FelixTrujillo/ESP32-DAQ/DAQ-Interface/Assets/Chart And Graph/Textures/back_black.png

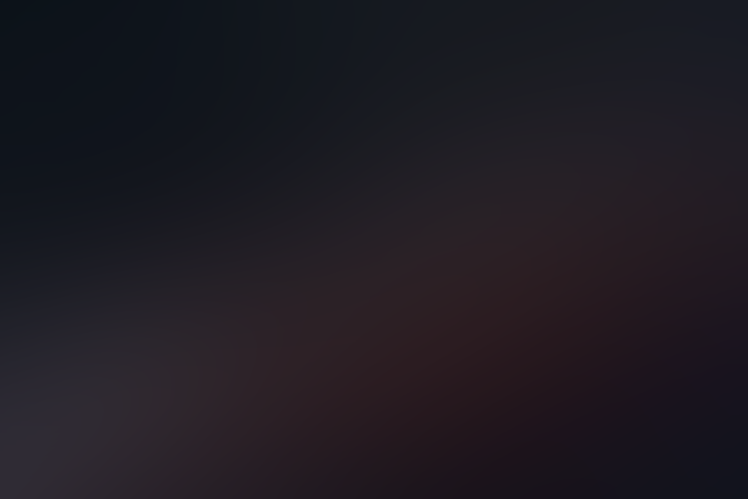
DAQ-Interface/Assets/Chart And Graph/Textures/back_black.png
