FelixTrujillo/ESP32-DAQ/DAQ-Interface/Assets/Chart And Graph/Textures/back_paper.png

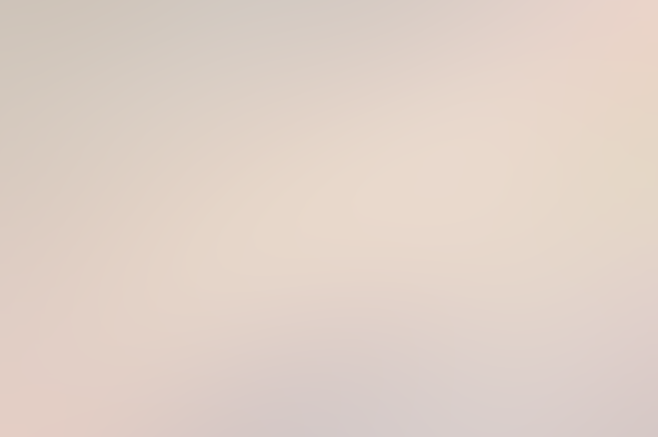
DAQ-Interface/Assets/Chart And Graph/Textures/back_paper.png
