FelixTrujillo/ESP32-DAQ/DAQ-Interface/Assets/Chart And Graph/Textures/background2.png

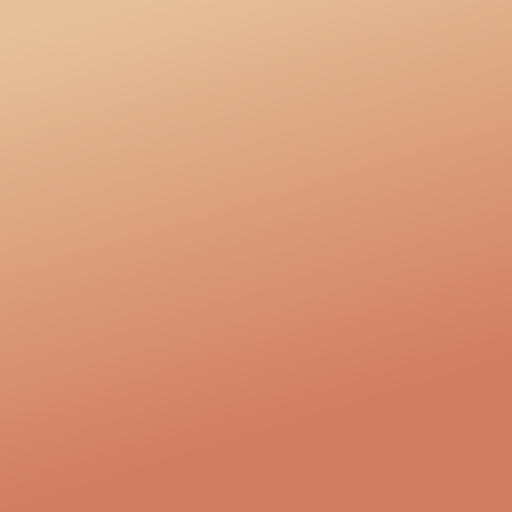
DAQ-Interface/Assets/Chart And Graph/Textures/background2.png
