FelixTrujillo/ESP32-DAQ/DAQ-Interface/Assets/Chart And Graph/Textures/backround2.png

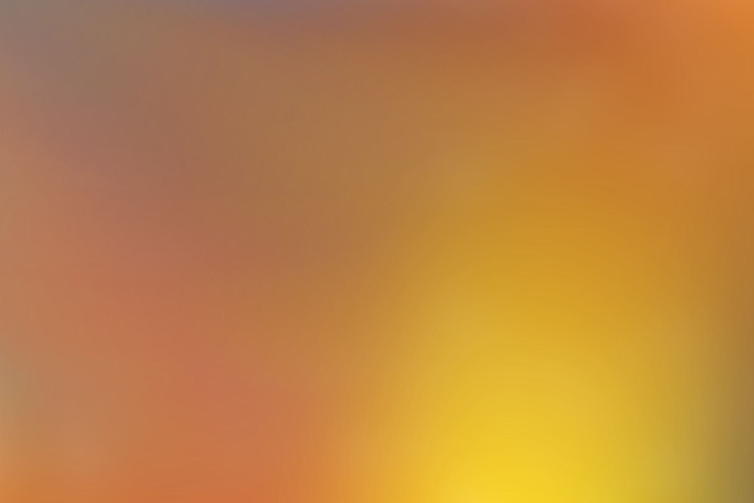
DAQ-Interface/Assets/Chart And Graph/Textures/backround2.png
