FelixTrujillo/ESP32-DAQ/DAQ-Interface/Assets/Chart And Graph/Textures/backround4.png

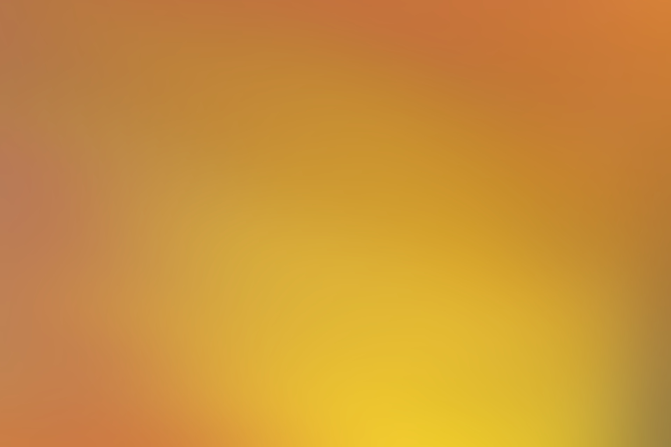
DAQ-Interface/Assets/Chart And Graph/Textures/backround4.png
