FelixTrujillo/ESP32-DAQ/DAQ-Interface/Assets/Chart And Graph/Textures/backround5.png

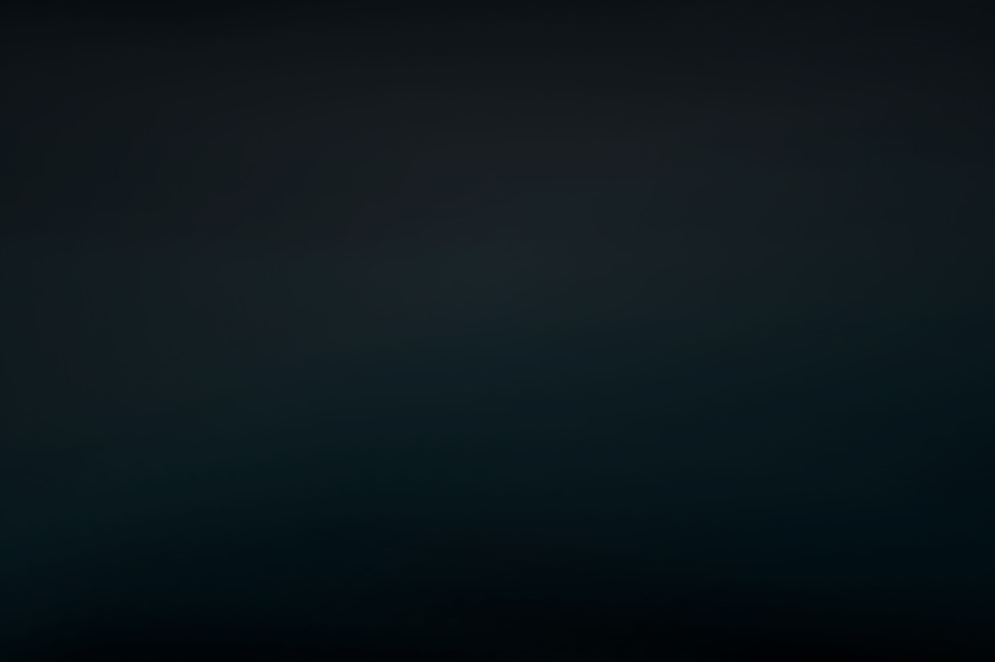
DAQ-Interface/Assets/Chart And Graph/Textures/backround5.png
