FelixTrujillo/ESP32-DAQ/DAQ-Interface/Assets/Chart And Graph/Textures/Bars/bar2.png

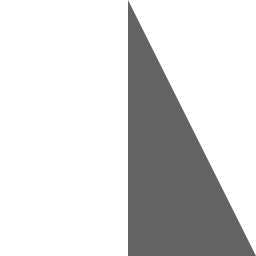
DAQ-Interface/Assets/Chart And Graph/Textures/Bars/bar2.png
