FelixTrujillo/ESP32-DAQ/DAQ-Interface/Assets/Chart And Graph/Textures/Bars/bar4.png

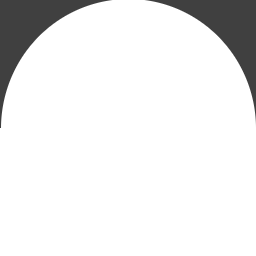
DAQ-Interface/Assets/Chart And Graph/Textures/Bars/bar4.png
