FelixTrujillo/ESP32-DAQ/DAQ-Interface/Assets/Chart And Graph/Textures/pieShade2.png

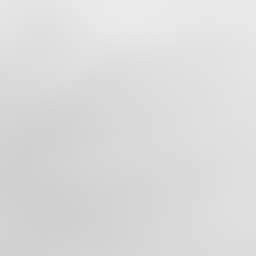
DAQ-Interface/Assets/Chart And Graph/Textures/pieShade2.png
