FelixTrujillo/ESP32-DAQ/DAQ-Interface/Assets/Chart And Graph/Textures/Points/CirclePoint.png

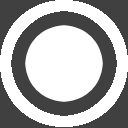
DAQ-Interface/Assets/Chart And Graph/Textures/Points/CirclePoint.png
