FelixTrujillo/ESP32-DAQ/DAQ-Interface/Assets/Chart And Graph/Textures/Points/Shade.png

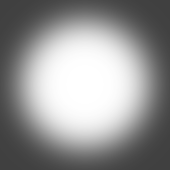
DAQ-Interface/Assets/Chart And Graph/Textures/Points/Shade.png
