FelixTrujillo/ESP32-DAQ/DAQ-Interface/Assets/Chart And Graph/Textures/Points/SimplePoint.png

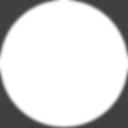
DAQ-Interface/Assets/Chart And Graph/Textures/Points/SimplePoint.png
