FelixTrujillo/ESP32-DAQ/DAQ-Interface/Assets/Chart And Graph/Themes/Common/Textures/borderPoint.png

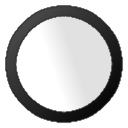
DAQ-Interface/Assets/Chart And Graph/Themes/Common/Textures/borderPoint.png
