FelixTrujillo/ESP32-DAQ/DAQ-Interface/Assets/Chart And Graph/Themes/Common/Textures/cc0-license/content/earth-earth-at-night-night-lights-41949.png

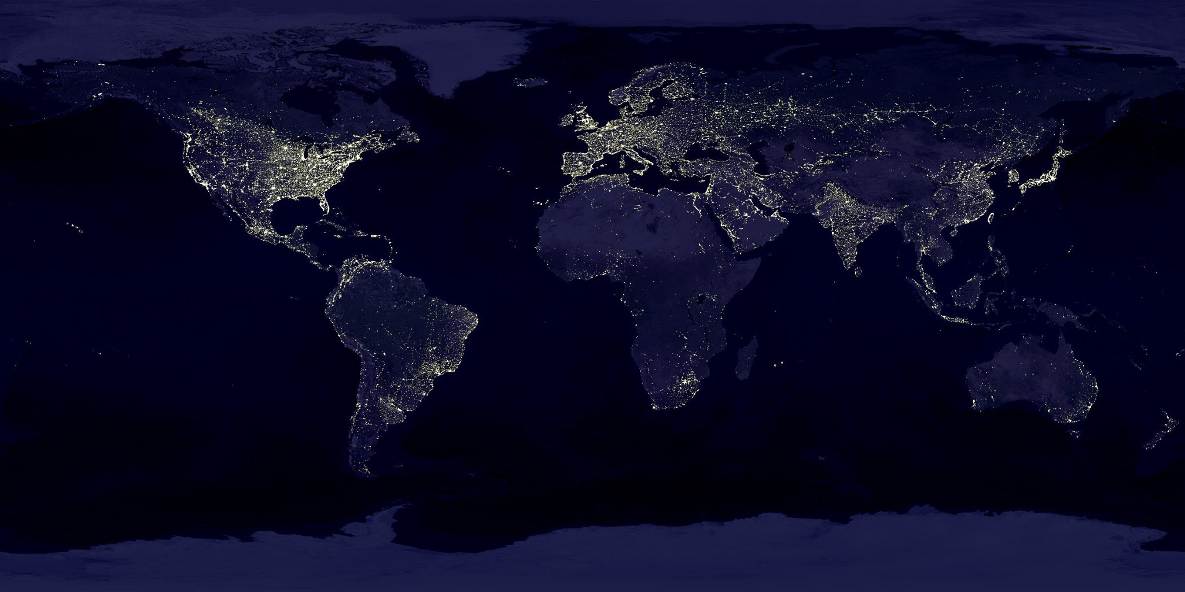
DAQ-Interface/Assets/Chart And Graph/Themes/Common/Textures/cc0-license/content/earth-earth-at-night-night-lights-41949.png
