FelixTrujillo/ESP32-DAQ/DAQ-Interface/Assets/Chart And Graph/Themes/Common/Textures/cc0-license/content/light-abstract-fire-heat.png

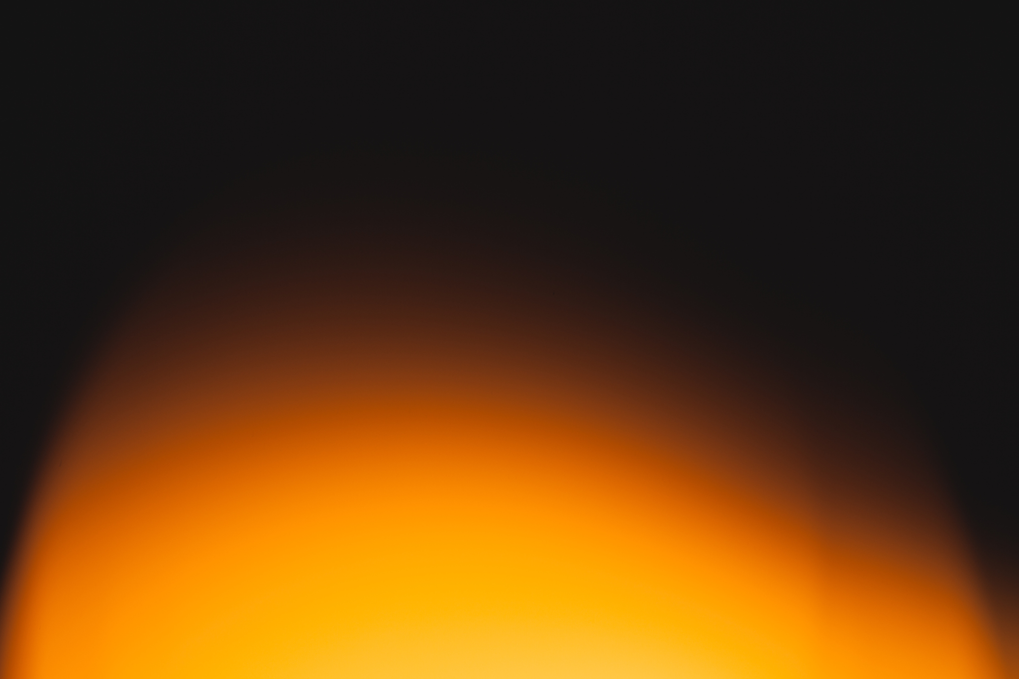
DAQ-Interface/Assets/Chart And Graph/Themes/Common/Textures/cc0-license/content/light-abstract-fire-heat.png
