FelixTrujillo/ESP32-DAQ/DAQ-Interface/Assets/Chart And Graph/Themes/Common/Textures/cc0-license/content/pexels-photo (1).png

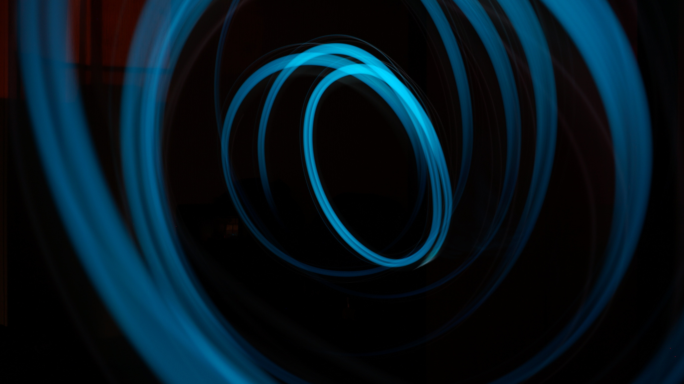
DAQ-Interface/Assets/Chart And Graph/Themes/Common/Textures/cc0-license/content/pexels-photo (1).png
