FelixTrujillo/ESP32-DAQ/DAQ-Interface/Assets/Chart And Graph/Themes/Common/Textures/cc0-license/content/yellow_notebook_paper_by_orangedotgreen.png

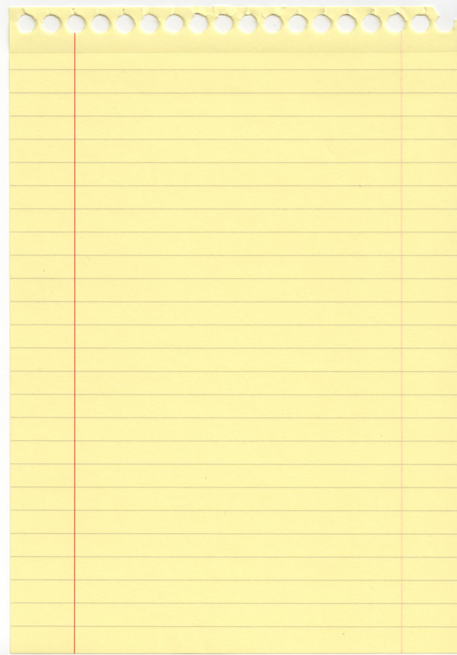
DAQ-Interface/Assets/Chart And Graph/Themes/Common/Textures/cc0-license/content/yellow_notebook_paper_by_orangedotgreen.png
