FelixTrujillo/ESP32-DAQ/DAQ-Interface/Assets/Chart And Graph/Themes/Common/Textures/T_Grid_floor2.png

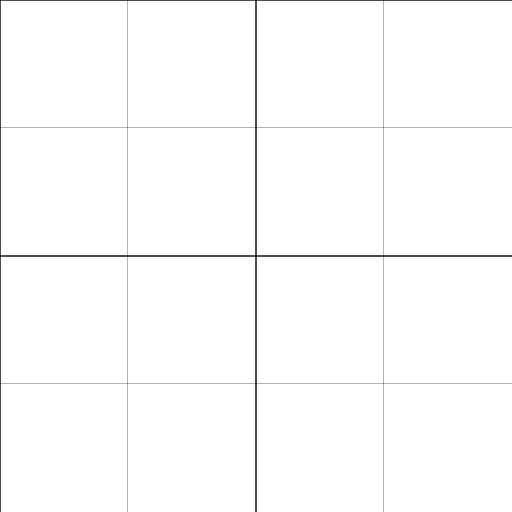
DAQ-Interface/Assets/Chart And Graph/Themes/Common/Textures/T_Grid_floor2.png
