FelixTrujillo/ESP32-DAQ/DAQ-Interface/Assets/Chart And Graph/Themes/Common/Textures/T_Hex.png

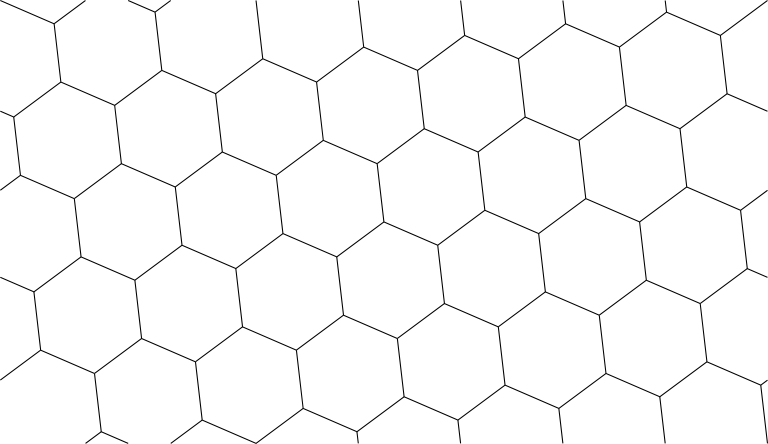
DAQ-Interface/Assets/Chart And Graph/Themes/Common/Textures/T_Hex.png
