FelixTrujillo/ESP32-DAQ/DAQ-Interface/Assets/Dark UI/Free/32 Light 2.png

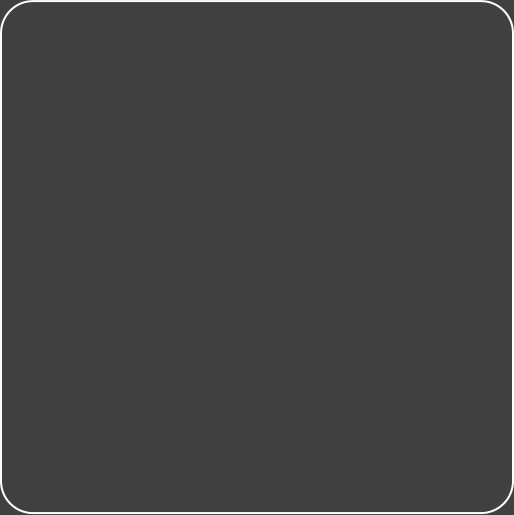
DAQ-Interface/Assets/Dark UI/Free/32 Light 2.png
