FelixTrujillo/ESP32-DAQ/DAQ-Interface/Assets/Dark UI/Free/128 Light 2.png

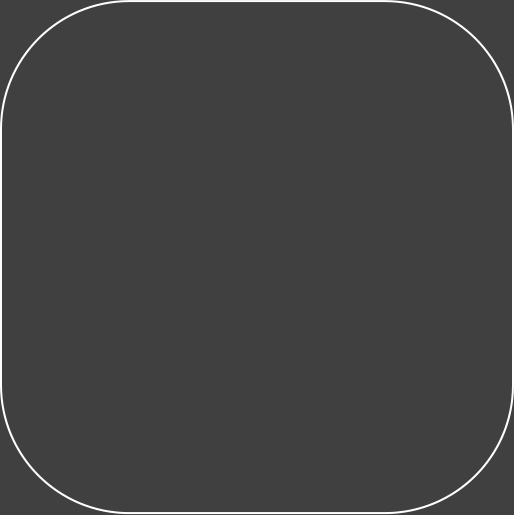
DAQ-Interface/Assets/Dark UI/Free/128 Light 2.png
