FelixTrujillo/ESP32-DAQ/DAQ-Interface/Assets/Dark UI/Free/Bell.png

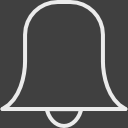
DAQ-Interface/Assets/Dark UI/Free/Bell.png
