FelixTrujillo/ESP32-DAQ/DAQ-Interface/Assets/Dark UI/Free/CIRCLE2PXLAR.png

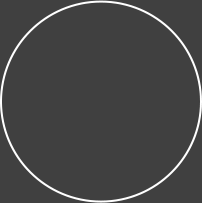
DAQ-Interface/Assets/Dark UI/Free/CIRCLE2PXLAR.png
