FelixTrujillo/ESP32-DAQ/DAQ-Interface/Assets/Dark UI/Free/Close BTN.png

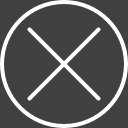
DAQ-Interface/Assets/Dark UI/Free/Close BTN.png
