FelixTrujillo/ESP32-DAQ/DAQ-Interface/Assets/Dark UI/Free/Coin.png

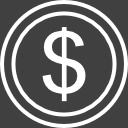
DAQ-Interface/Assets/Dark UI/Free/Coin.png
