FelixTrujillo/ESP32-DAQ/DAQ-Interface/Assets/Dark UI/Free/Down Arrow.png

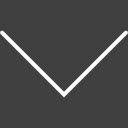
DAQ-Interface/Assets/Dark UI/Free/Down Arrow.png
