FelixTrujillo/ESP32-DAQ/DAQ-Interface/Assets/Dark UI/Free/Down BTN.png

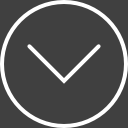
DAQ-Interface/Assets/Dark UI/Free/Down BTN.png
