FelixTrujillo/ESP32-DAQ/DAQ-Interface/Assets/Dark UI/Free/Facebook 2.png

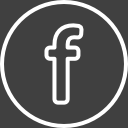
DAQ-Interface/Assets/Dark UI/Free/Facebook 2.png
