FelixTrujillo/ESP32-DAQ/DAQ-Interface/Assets/Dark UI/Free/Facebook.png

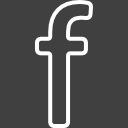
DAQ-Interface/Assets/Dark UI/Free/Facebook.png
