FelixTrujillo/ESP32-DAQ/DAQ-Interface/Assets/Dark UI/Free/Gem.png

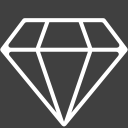
DAQ-Interface/Assets/Dark UI/Free/Gem.png
