FelixTrujillo/ESP32-DAQ/DAQ-Interface/Assets/Dark UI/Free/Heart.png

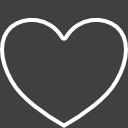
DAQ-Interface/Assets/Dark UI/Free/Heart.png
