FelixTrujillo/ESP32-DAQ/DAQ-Interface/Assets/Dark UI/Free/Info.png

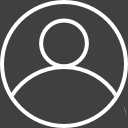
DAQ-Interface/Assets/Dark UI/Free/Info.png
