FelixTrujillo/ESP32-DAQ/DAQ-Interface/Assets/Dark UI/Free/Left Arrow.png

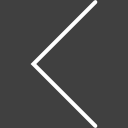
DAQ-Interface/Assets/Dark UI/Free/Left Arrow.png
