FelixTrujillo/ESP32-DAQ/DAQ-Interface/Assets/Dark UI/Free/Left BTN.png

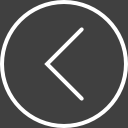
DAQ-Interface/Assets/Dark UI/Free/Left BTN.png
