FelixTrujillo/ESP32-DAQ/DAQ-Interface/Assets/Dark UI/Free/Lock.png

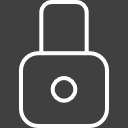
DAQ-Interface/Assets/Dark UI/Free/Lock.png
