FelixTrujillo/ESP32-DAQ/DAQ-Interface/Assets/Dark UI/Free/Messages.png

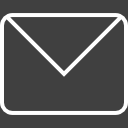
DAQ-Interface/Assets/Dark UI/Free/Messages.png
