FelixTrujillo/ESP32-DAQ/DAQ-Interface/Assets/Dark UI/Free/Missions.png

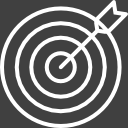
DAQ-Interface/Assets/Dark UI/Free/Missions.png
