FelixTrujillo/ESP32-DAQ/DAQ-Interface/Assets/Dark UI/Free/Music.png

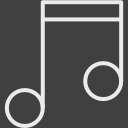
DAQ-Interface/Assets/Dark UI/Free/Music.png
