FelixTrujillo/ESP32-DAQ/DAQ-Interface/Assets/Dark UI/Free/Ranks.png

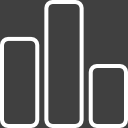
DAQ-Interface/Assets/Dark UI/Free/Ranks.png
