FelixTrujillo/ESP32-DAQ/DAQ-Interface/Assets/Dark UI/Free/Right Arrow.png

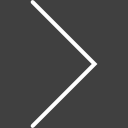
DAQ-Interface/Assets/Dark UI/Free/Right Arrow.png
