FelixTrujillo/ESP32-DAQ/DAQ-Interface/Assets/Dark UI/Free/Right BTN.png

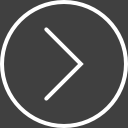
DAQ-Interface/Assets/Dark UI/Free/Right BTN.png
