FelixTrujillo/ESP32-DAQ/DAQ-Interface/Assets/Dark UI/Free/Settings.png

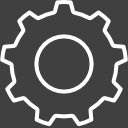
DAQ-Interface/Assets/Dark UI/Free/Settings.png
