FelixTrujillo/ESP32-DAQ/DAQ-Interface/Assets/Dark UI/Free/Shop.png

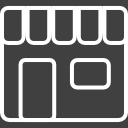
DAQ-Interface/Assets/Dark UI/Free/Shop.png
