FelixTrujillo/ESP32-DAQ/DAQ-Interface/Assets/Dark UI/Free/Sound.png

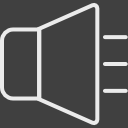
DAQ-Interface/Assets/Dark UI/Free/Sound.png
