FelixTrujillo/ESP32-DAQ/DAQ-Interface/Assets/Dark UI/Free/Star.png

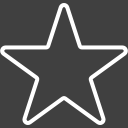
DAQ-Interface/Assets/Dark UI/Free/Star.png
