FelixTrujillo/ESP32-DAQ/DAQ-Interface/Assets/Dark UI/Free/Up Arrow.png

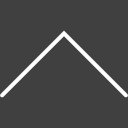
DAQ-Interface/Assets/Dark UI/Free/Up Arrow.png
