FelixTrujillo/ESP32-DAQ/DAQ-Interface/Assets/Dark UI/Free/Up BTN.png

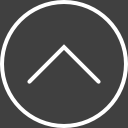
DAQ-Interface/Assets/Dark UI/Free/Up BTN.png
