FelixTrujillo/ESP32-DAQ/DAQ-Interface/Assets/Dark UI/Free/World.png

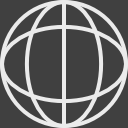
DAQ-Interface/Assets/Dark UI/Free/World.png
