FelixTrujillo/ESP32-DAQ/DAQ-Interface/Assets/Dark UI/Free/X.png

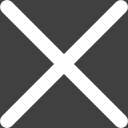
DAQ-Interface/Assets/Dark UI/Free/X.png
