FelixTrujillo/ESP32-DAQ/DAQ-Interface/Assets/Images/Bicineta_general.jpeg

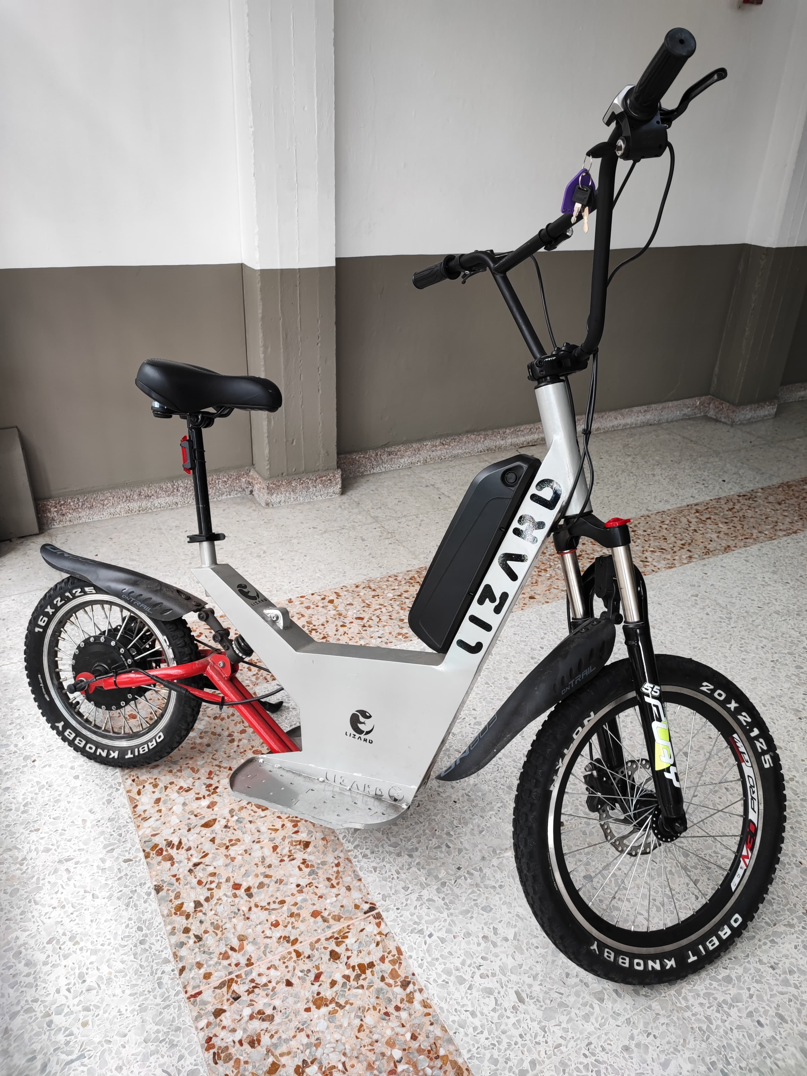
DAQ-Interface/Assets/Images/Bicineta_general.jpeg
