FelixTrujillo/ESP32-DAQ/Documentation/Images/Bicineta_backward.jpeg

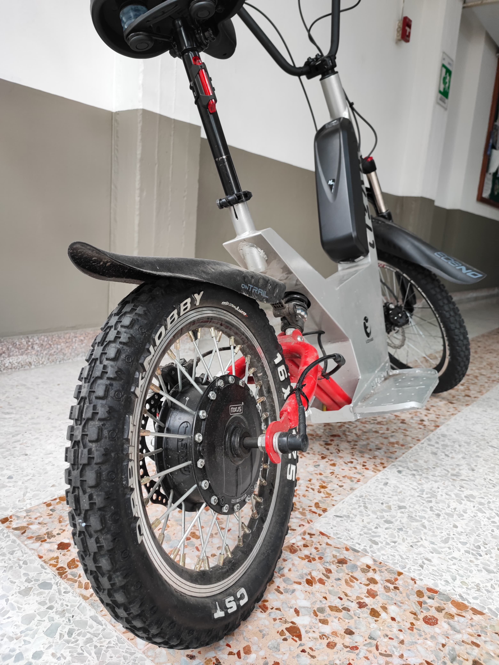
Documentation/Images/Bicineta_backward.jpeg
