FelixTrujillo/ESP32-DAQ/Documentation/Images/Bicineta_forward.jpeg

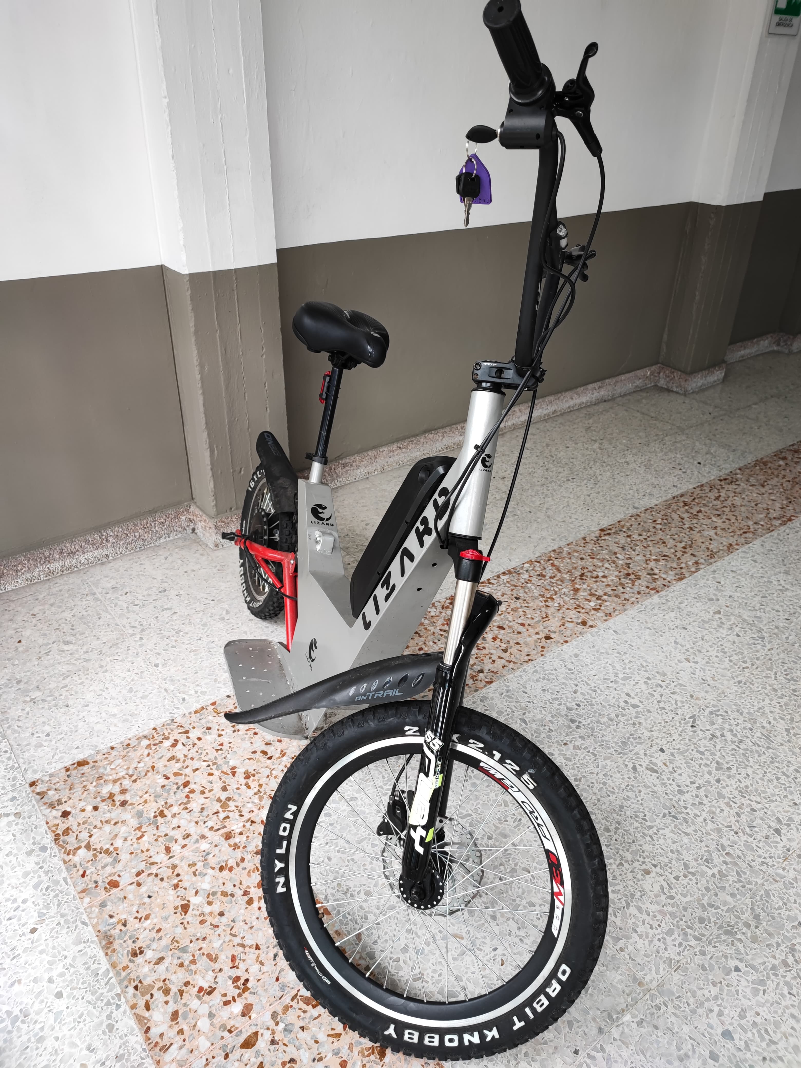
Documentation/Images/Bicineta_forward.jpeg
