FelixTrujillo/ESP32-DAQ/Documentation/Images/DAQ-Bicineta_render.png

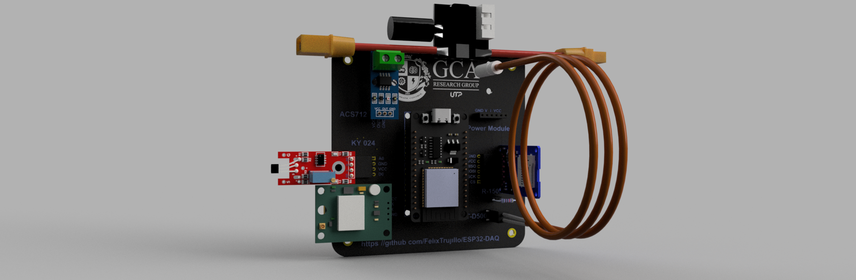
Documentation/Images/DAQ-Bicineta_render.png
