FelixTrujillo/ESP32-DAQ/Documentation/Images/DAQ_Bicineta_backward.jpeg

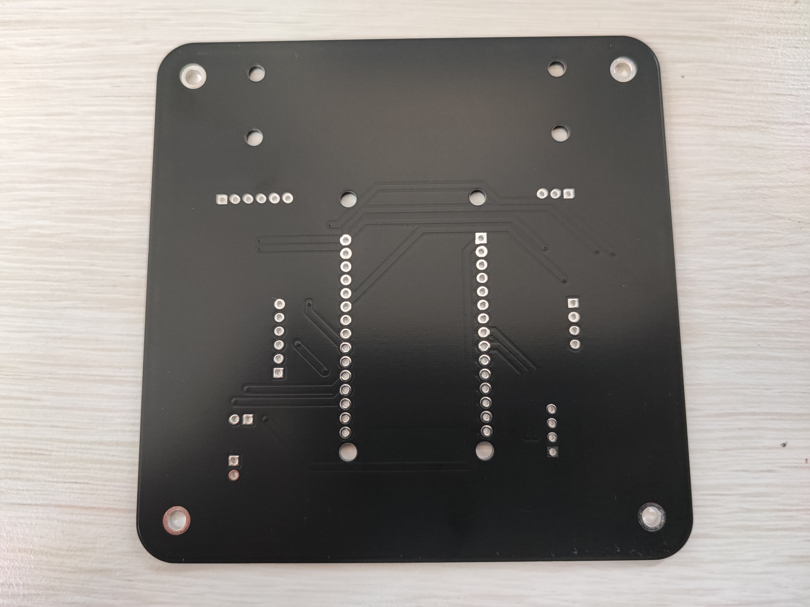
Documentation/Images/DAQ_Bicineta_backward.jpeg
