FelixTrujillo/ESP32-DAQ/Documentation/Images/DAQ_Bicineta_forward.jpeg

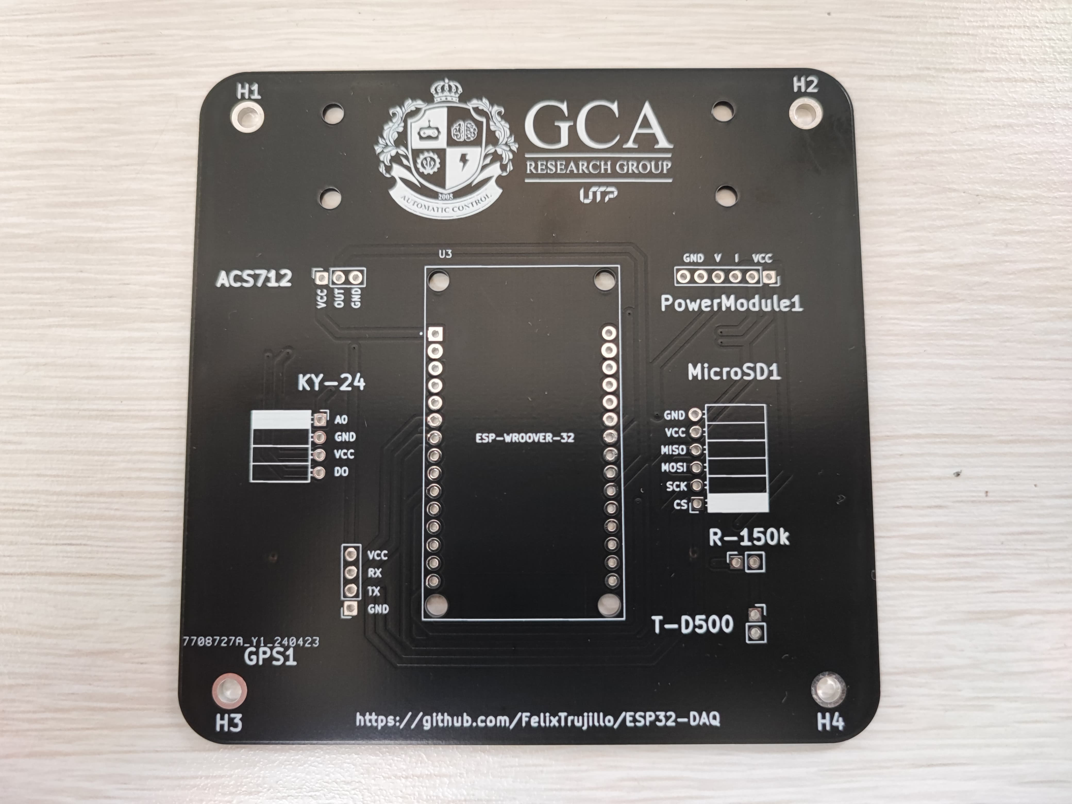
Documentation/Images/DAQ_Bicineta_forward.jpeg
