FelixTrujillo/ESP32-DAQ/Documentation/Images/Intarface/acceleration.png

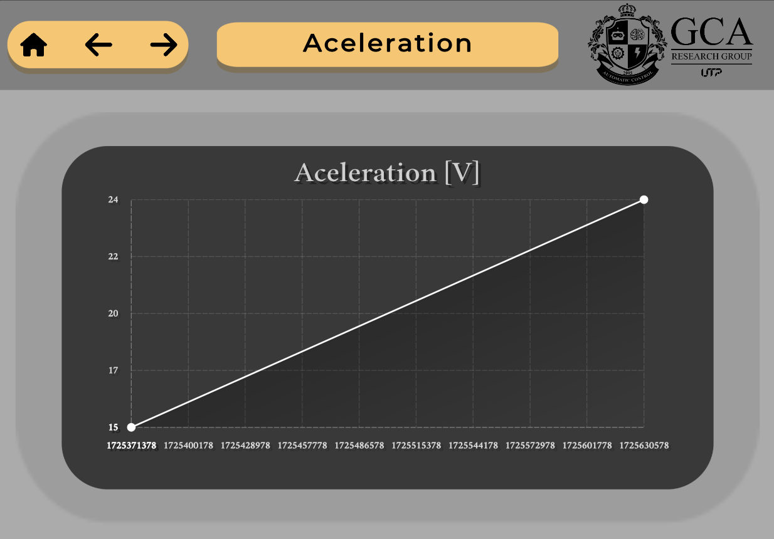
Documentation/Images/Intarface/acceleration.png
