FelixTrujillo/ESP32-DAQ/Documentation/Images/Intarface/brokerConfig.png

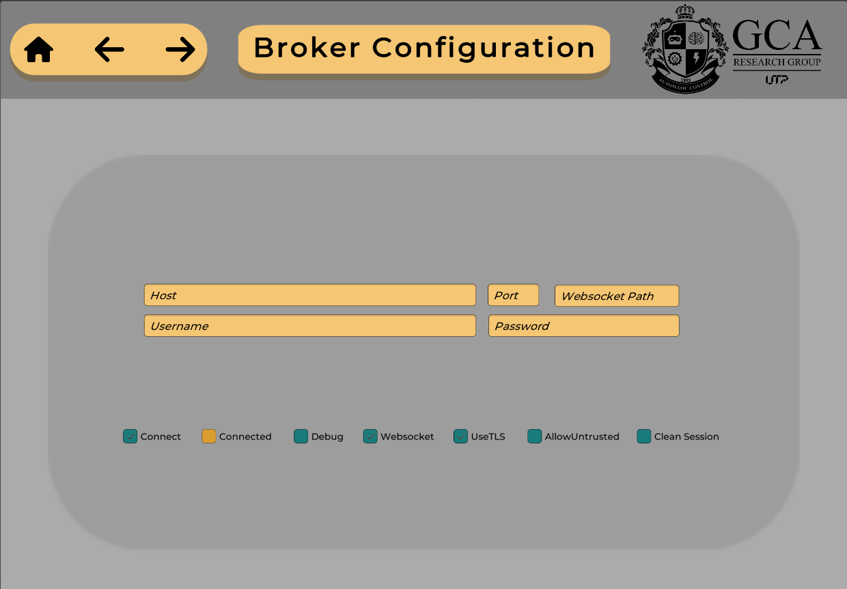
Documentation/Images/Intarface/brokerConfig.png
