FelixTrujillo/ESP32-DAQ/Documentation/Images/Intarface/current.png

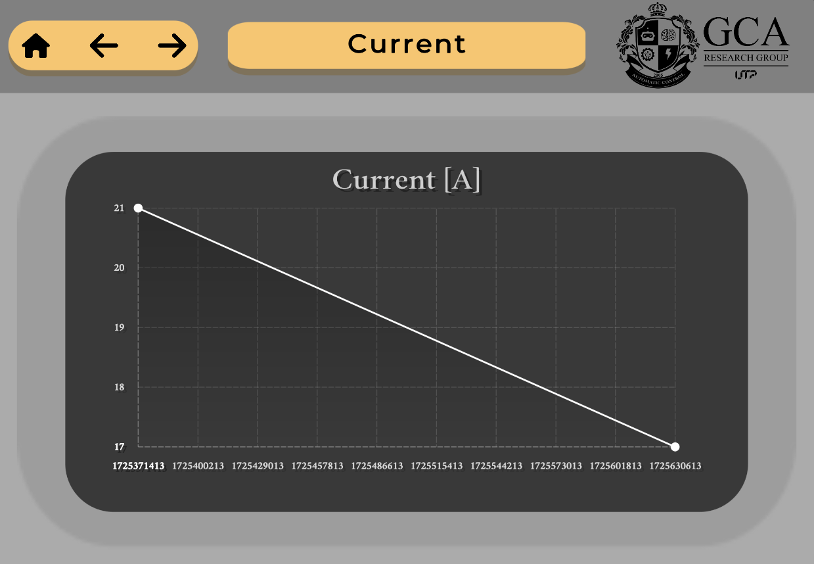
Documentation/Images/Intarface/current.png
