FelixTrujillo/ESP32-DAQ/Documentation/Images/Intarface/generalInformation.png

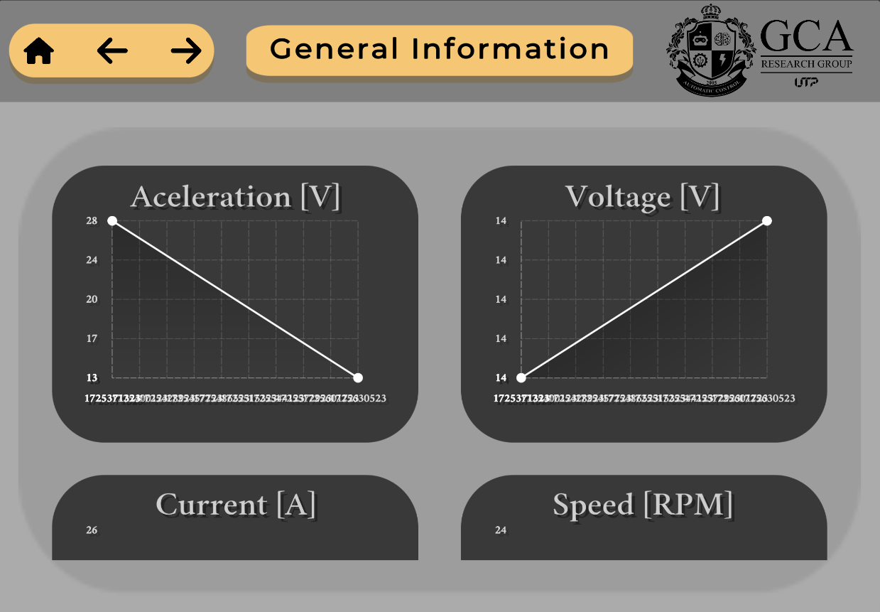
Documentation/Images/Intarface/generalInformation.png
