FelixTrujillo/ESP32-DAQ/Documentation/Images/Intarface/Loggin.png

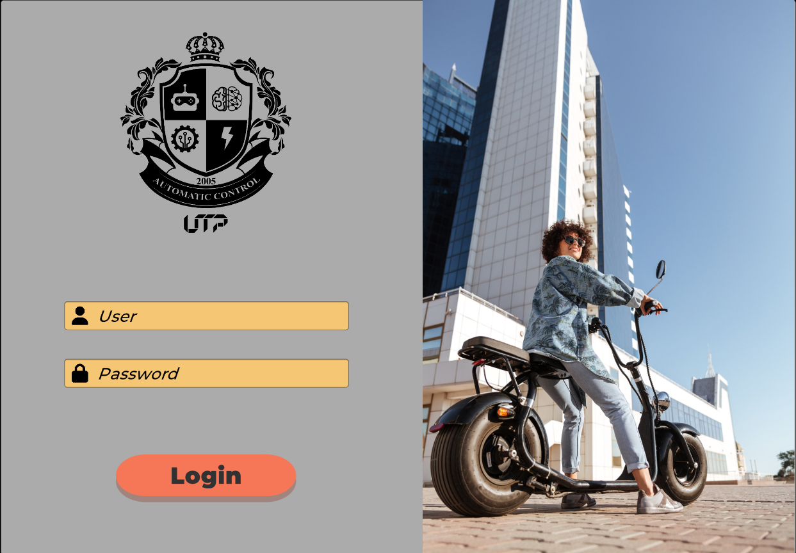
Documentation/Images/Intarface/Loggin.png
