FelixTrujillo/ESP32-DAQ/Documentation/Images/Intarface/Menu.png

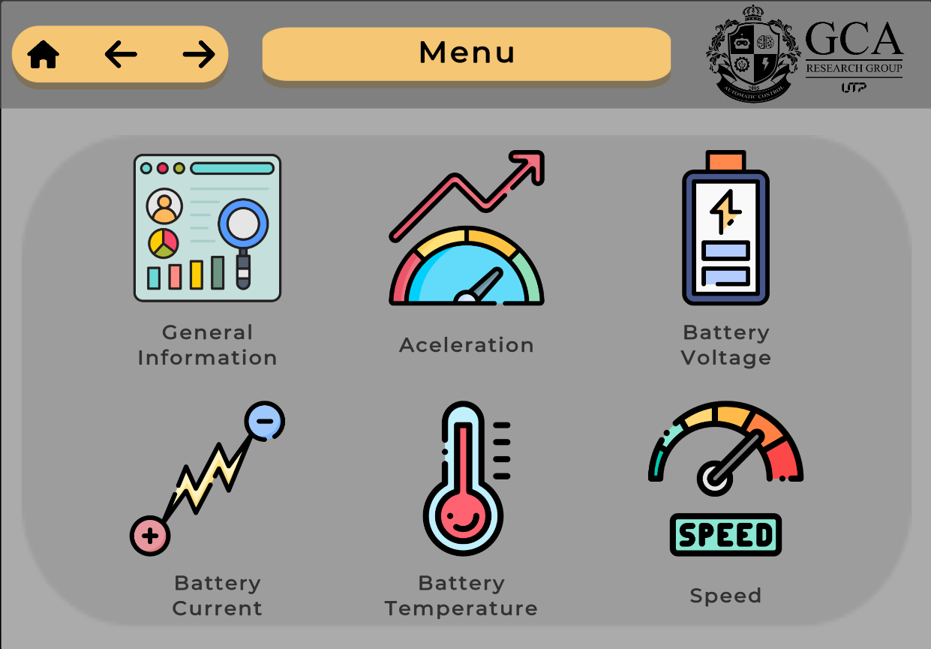
Documentation/Images/Intarface/Menu.png
