FelixTrujillo/ESP32-DAQ/DAQ-Interface/Assets/Chart And Graph/Themes/Common/Materials/Skybox/skybox1.png

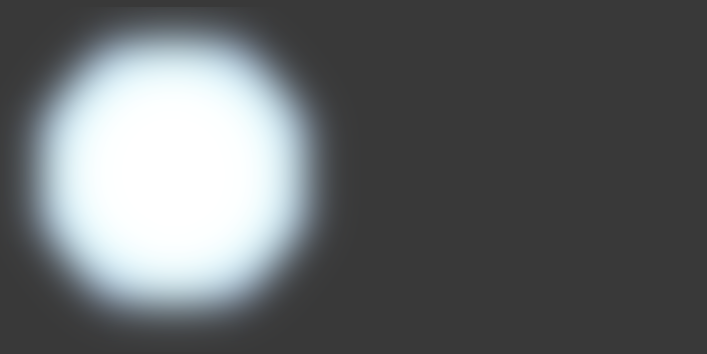
DAQ-Interface/Assets/Chart And Graph/Themes/Common/Materials/Skybox/skybox1.png
