FelixTrujillo/ESP32-DAQ/DAQ-Interface/Assets/Dark UI/Free/Inventory.png

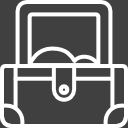
DAQ-Interface/Assets/Dark UI/Free/Inventory.png
