FelixTrujillo/ESP32-DAQ/IdentificationCodes/Bicineta-PythonIdentification/ImgANN_prueba1/Corriente_normalizada_EstimacionvsReal.png

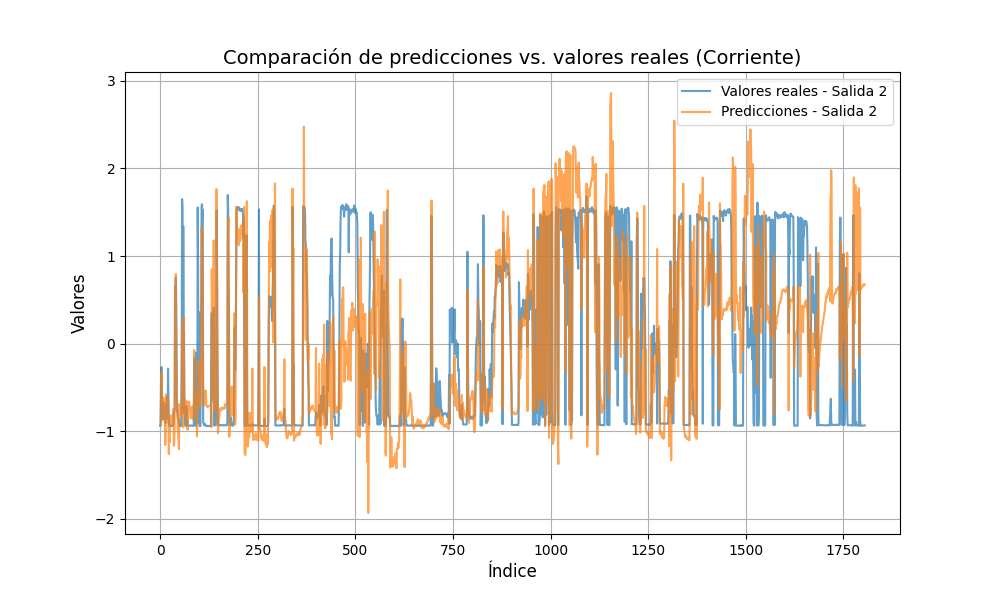
IdentificationCodes/Bicineta-PythonIdentification/ImgANN_prueba1/Corriente_normalizada_EstimacionvsReal.png
