FelixTrujillo/ESP32-DAQ/IdentificationCodes/Bicineta-PythonIdentification/ImgANN_prueba1/modelo.png

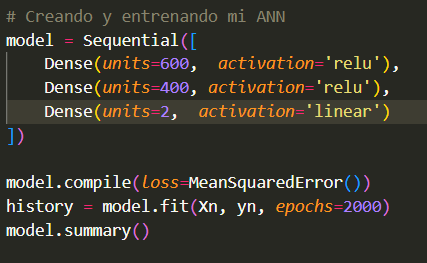
IdentificationCodes/Bicineta-PythonIdentification/ImgANN_prueba1/modelo.png
