FelixTrujillo/ESP32-DAQ/IdentificationCodes/Bicineta-PythonIdentification/ImgANN_prueba1/Perdidas.png

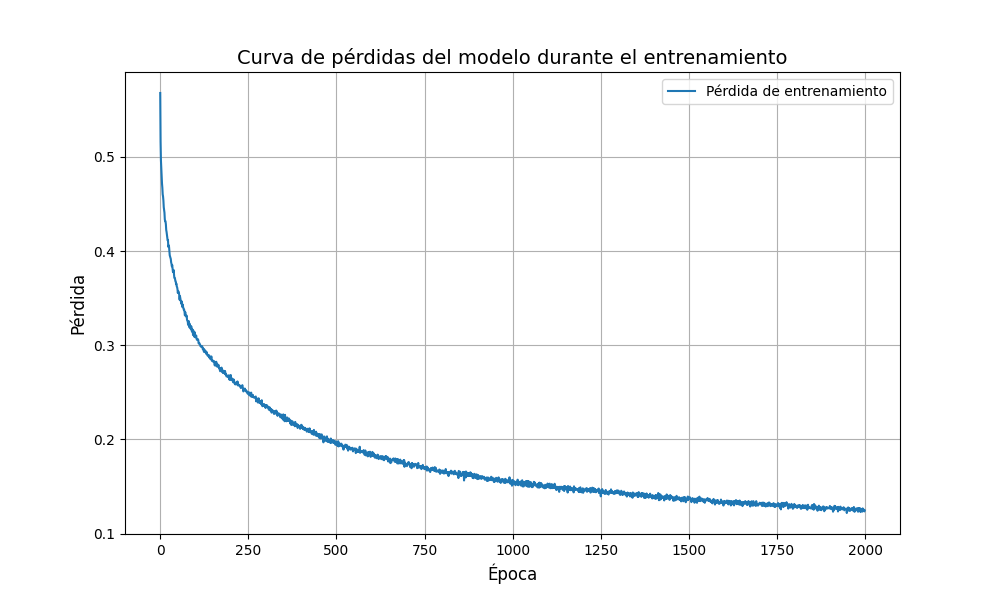
IdentificationCodes/Bicineta-PythonIdentification/ImgANN_prueba1/Perdidas.png
