FelixTrujillo/ESP32-DAQ/IdentificationCodes/Bicineta-PythonIdentification/ImgANN_prueba2/Corriente_normalizada_RealvsEstimacion.png

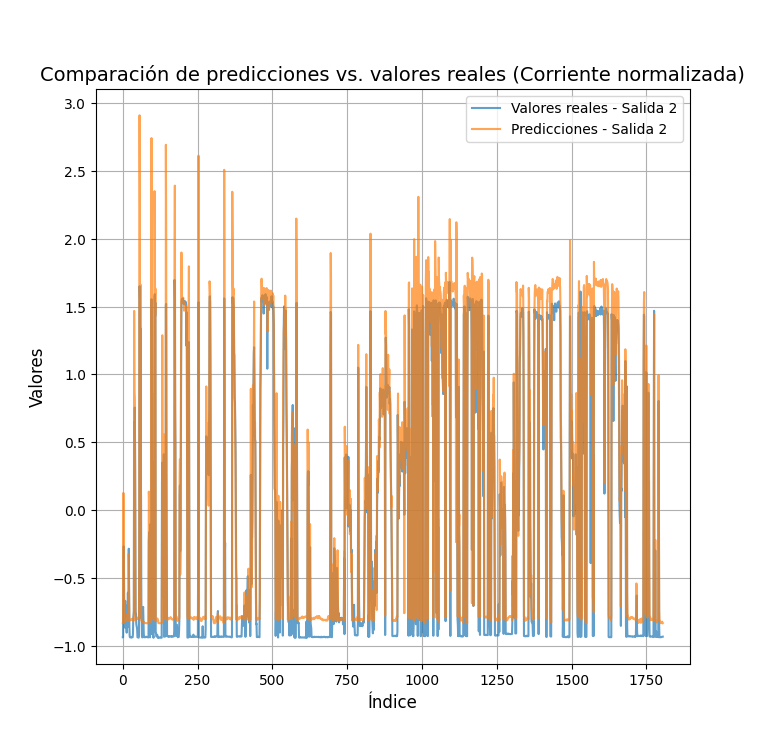
IdentificationCodes/Bicineta-PythonIdentification/ImgANN_prueba2/Corriente_normalizada_RealvsEstimacion.png
