FelixTrujillo/ESP32-DAQ/IdentificationCodes/Bicineta-PythonIdentification/ImgANN_prueba2/Dispersion.png

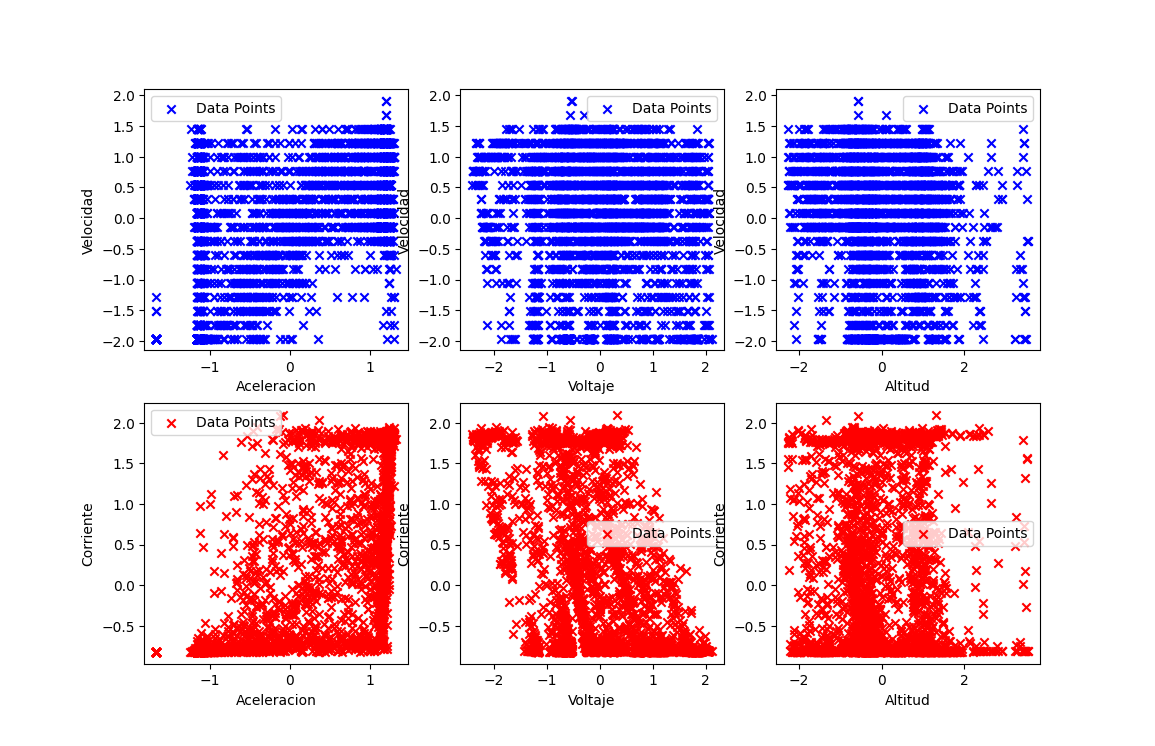
IdentificationCodes/Bicineta-PythonIdentification/ImgANN_prueba2/Dispersion.png
