FelixTrujillo/ESP32-DAQ/IdentificationCodes/Bicineta-PythonIdentification/ImgANN_prueba2/Perdida.png

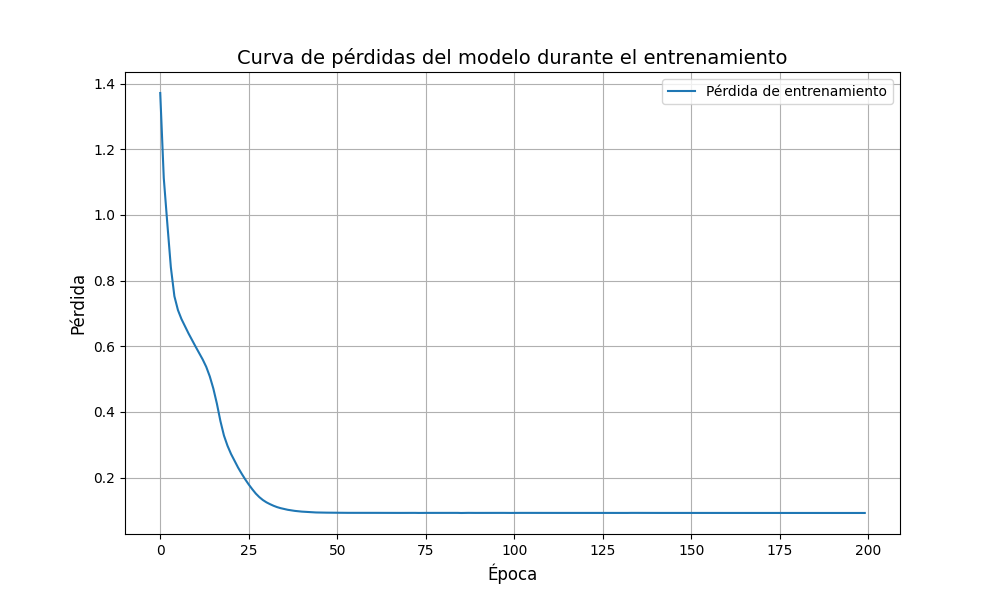
IdentificationCodes/Bicineta-PythonIdentification/ImgANN_prueba2/Perdida.png
