FelixTrujillo/ESP32-DAQ/IdentificationCodes/Bicineta-PythonIdentification/ImgANN_prueba2/Velocidad_RealvsEstimacion.png

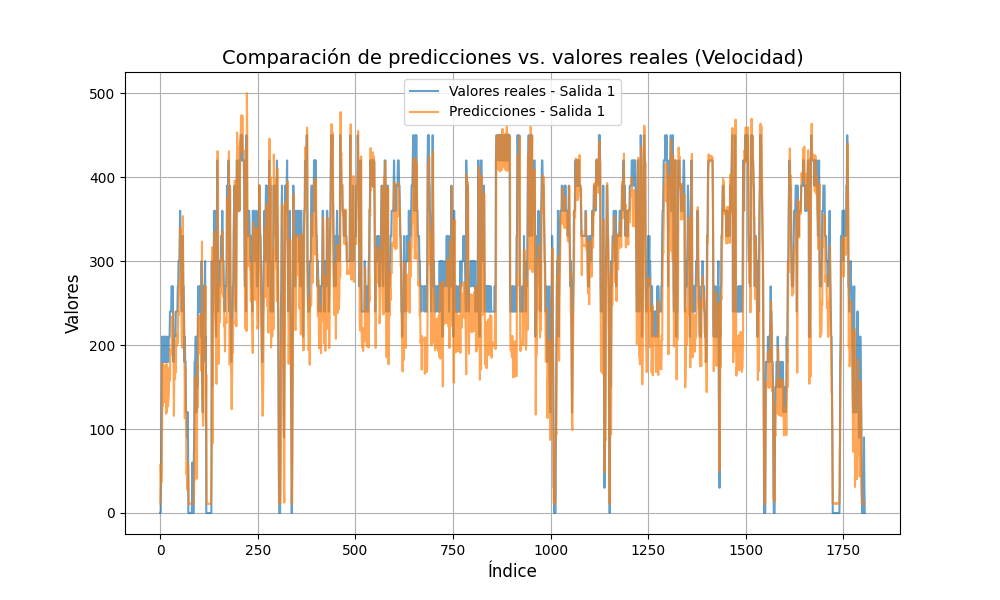
IdentificationCodes/Bicineta-PythonIdentification/ImgANN_prueba2/Velocidad_RealvsEstimacion.png
